El-Tomaz/CONTROLE-IR-GREL/Arduino_Blynk_MQTT/arduino_secrets.h

/* Fill in information from Blynk Device Info here.
   Read More: https://bit.ly/BlynkSimpleAuth
*/
#define BLYNK_TEMPLATE_ID "TMPL2x7YYtIFc"
#define BLYNK_TEMPLATE_NAME "Controle GREL"
#define BLYNK_AUTH_TOKEN "yMd0juu33lNdFQ_nCQVAi1ru5th6HobZ"
/* Change the default Blynk server. Applicable for users with a white label plan. */
//#define BLYNK_MQTT_BROKER       "blynk.cloud"
//#define BLYNK_MQTT_PORT         8883

/* Disable Secure TLS connection. Only use it for testing purposes. */
//#define BLYNK_MQTT_UNSECURE
